acarmony1/comal80/C64/comal-80.png

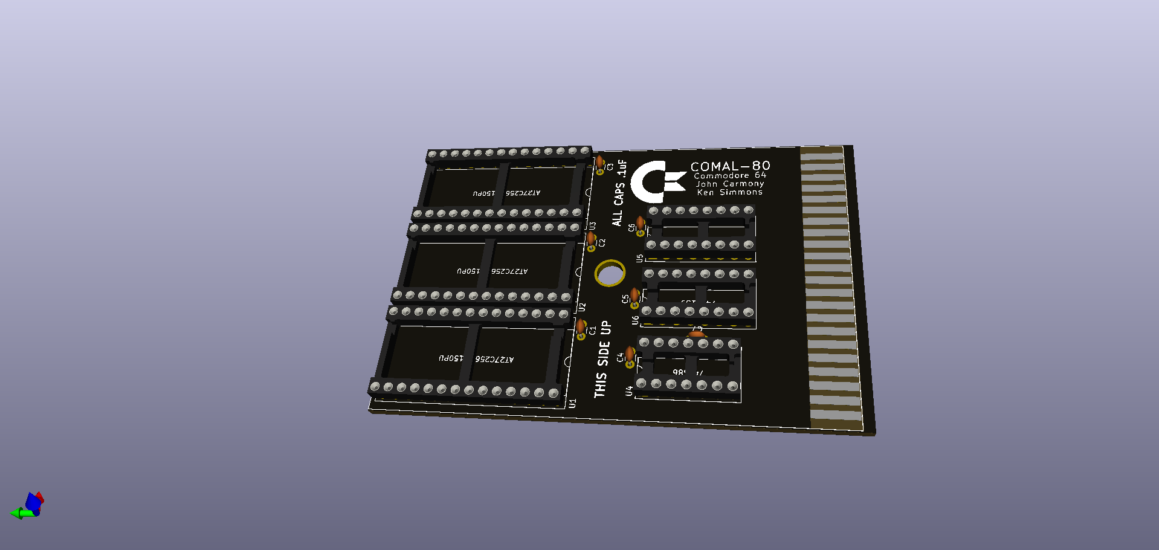
C64/comal-80.png
