acarmony1/comal80/C64/reference/comal80cartridgepictures/DSC02216.JPG

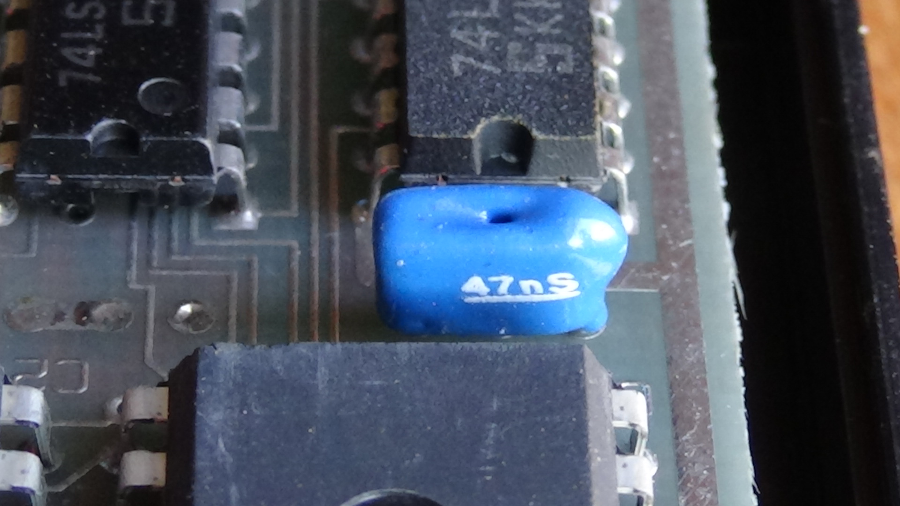
C64/reference/comal80cartridgepictures/DSC02216.JPG
