acarmony1/comal80/C64/reference/comal80cartridgepictures/DSC02217.JPG

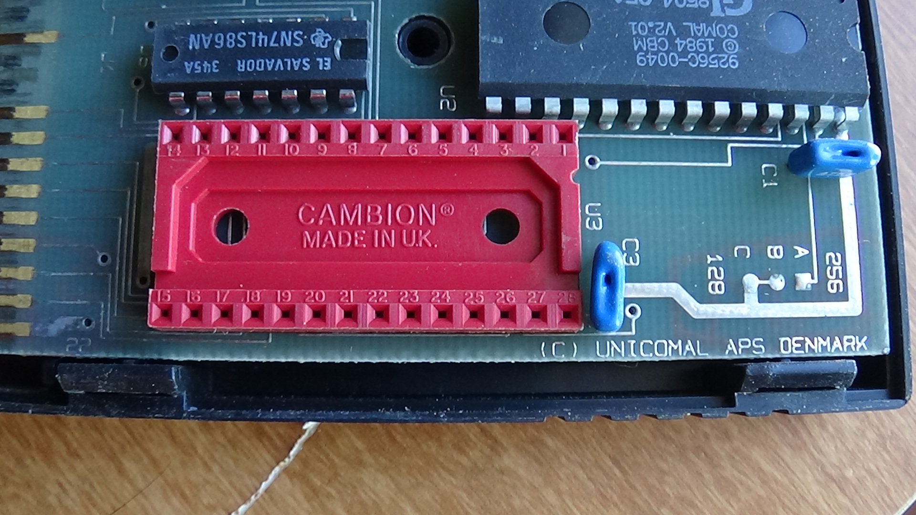
C64/reference/comal80cartridgepictures/DSC02217.JPG
