acarmony1/comal80/C64/reference/comal80cartridgepictures/DSC02220.JPG

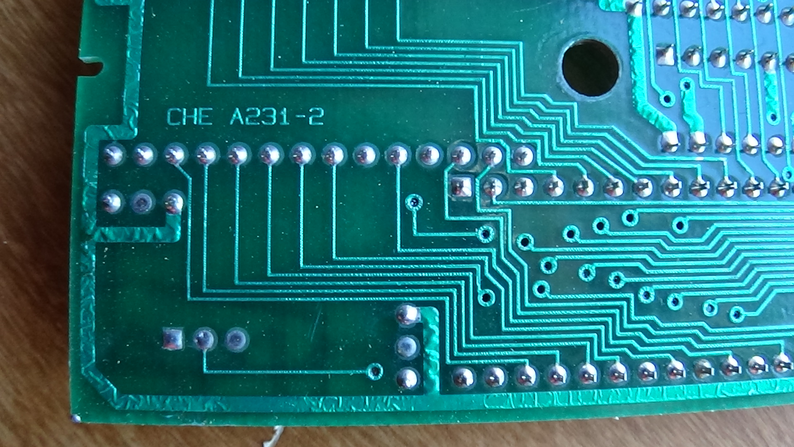
C64/reference/comal80cartridgepictures/DSC02220.JPG
